BadRAM/MatrixBuddy/MatrixBuddyV2Firmware/SpriteData.h

int Smile[4] ={
  B00000000,
  B00100100,
  B00011000,
  B00000000
};

int Talk[4] ={
  B00000000,
  B00111100,
  B00011000,
  B00000000
};

int Sing[4] ={
  B00111100,
  B00100100,
  B00011000,
  B00000000
};

int TalkShut[4] ={
  B00000000,
  B00011000,
  B00000000,
  B00000000
};

int Mischief[4] ={
  B00000000,
  B00101010,
  B00010100,
  B00000000
};

int Cat[4] ={
  B00000000,
  B01000010,
  B10011001,
  B01100110
};

int Grin[4] ={
  B00000000,
  B01000010,
  B00111100,
  B00000000
};

int Fangs[4] ={
  B00000000,
  B01000010,
  B00111100,
  B00100000
};

int Neutral[4] ={
  B00000000,
  B00000000,
  B00111100,
  B00000000
};

int Pout[4] ={
  B00000000,
  B00011000,
  B00100100,
  B00000000
};

int Uncertain[4] ={
  B00000000,
  B00010100,
  B00101000,
  B00000000
};

int Yawn1[4] ={
  B00000000,
  B00111100,
  B00000000,
  B00000000
};

int Yawn2[4] ={
  B00000000,
  B00111100,
  B00111100,
  B00000000
};

int Yawn3[4] ={
  B00000000,
  B00111100,
  B00100100,
  B00011000
};

int Yawn4[4] ={
  B00111100,
  B00100100,
  B00100100,
  B00011000
};

int SleepMouth[4] ={
  B00000000,
  B00000000,
  B00011000,
  B00000000
};

int Eyes[4] ={
  B00000000,
  B00100100,
  B01100110,
  B00100100
};

int Wink1[4] ={
  B00000000,
  B00100000,
  B01100110,
  B00100100
};

int Wink2[4] ={
  B00000000,
  B00100000,
  B01100000,
  B00100110
};

int Blink1[4] ={
  B00000000,
  B00000000,
  B01100110,
  B00100100
};

int Blink2[4] ={
  B00000000,
  B00000000,
  B00000000,
  B01100110
};

int Squint[4] ={
  B00000000,
  B00000000,
  B01100110,
  B00000000
};

int LookUp[4] ={
  B00100100,
  B00100100,
  B01100110,
  B00000000
};

int LookLeft[4] ={
  B00000000,
  B01001000,
  B01101100,
  B01001000
};

int LookRight[4] ={
  B00000000,
  B00010010,
  B00110110,
  B00010010
};

int BrightnessIcon[4] ={
  B00000000,
  B01010000,
  B00100000,
  B01010000
};

int SleepThreshIcon[4] ={
  B00000000,
  B00100000,
  B01000000,
  B00100000
};

int MaruEksu[4] ={
  B00000000,
  B01000101,
  B10100010,
  B01000101
};
