BadRAM/MatrixBuddy/MatrixBuddyFirmware/SpriteData.h

const int Smile[4] ={
  B00000000,
  B00100100,
  B00011000,
  B00000000
};

const int Talk[4] ={
  B00000000,
  B00111100,
  B00011000,
  B00000000
};

const int Sing[4] ={
  B00111100,
  B00100100,
  B00011000,
  B00000000
};

const int TalkShut[4] ={
  B00000000,
  B00011000,
  B00000000,
  B00000000
};

const int Mischief[4] ={
  B00000000,
  B00101010,
  B00010100,
  B00000000
};

const int Cat[4] ={
  B00000000,
  B01000010,
  B10011001,
  B01100110
};

const int Grin[4] ={
  B00000000,
  B01000010,
  B00111100,
  B00000000
};

const int Fangs[4] ={
  B00000000,
  B01000010,
  B00111100,
  B00100000
};

const int Neutral[4] ={
  B00000000,
  B00000000,
  B00111100,
  B00000000
};

const int Pout[4] ={
  B00000000,
  B00011000,
  B00100100,
  B00000000
};

const int Uncertain[4] ={
  B00000000,
  B00010100,
  B00101000,
  B00000000
};

const int Yawn1[4] ={
  B00000000,
  B00111100,
  B00000000,
  B00000000
};

const int Yawn2[4] ={
  B00000000,
  B00111100,
  B00111100,
  B00000000
};

const int Yawn3[4] ={
  B00000000,
  B00111100,
  B00100100,
  B00011000
};

const int Yawn4[4] ={
  B00111100,
  B00100100,
  B00100100,
  B00011000
};

const int SleepMouth[4] ={
  B00000000,
  B00000000,
  B00011000,
  B00000000
};

const int Eyes[4] ={
  B00000000,
  B00100100,
  B01100110,
  B00100100
};

const int Wink1[4] ={
  B00000000,
  B00100000,
  B01100110,
  B00100100
};

const int Wink2[4] ={
  B00000000,
  B00100000,
  B01100000,
  B00100110
};

const int Blink1[4] ={
  B00000000,
  B00000000,
  B01100110,
  B00100100
};

const int Blink2[4] ={
  B00000000,
  B00000000,
  B00000000,
  B01100110
};

const int Squint[4] ={
  B00000000,
  B00000000,
  B01100110,
  B00000000
};

const int LookUp[4] ={
  B00100100,
  B00100100,
  B01100110,
  B00000000
};

const int LookLeft[4] ={
  B00000000,
  B01001000,
  B01101100,
  B01001000
};

const int LookRight[4] ={
  B00000000,
  B00010010,
  B00110110,
  B00010010
};

const int BrightnessIcon[4] ={
  B00000000,
  B01010000,
  B00100000,
  B01010000
};

const int SleepThreshIcon[4] ={
  B00000000,
  B00100000,
  B01000000,
  B00100000
};

const int MaruEksu[4] ={
  B00000000,
  B01000101,
  B10100010,
  B01000101
};
